DnyandevSawarkar/Mega_Project_Code/Images/arm_left.jpg

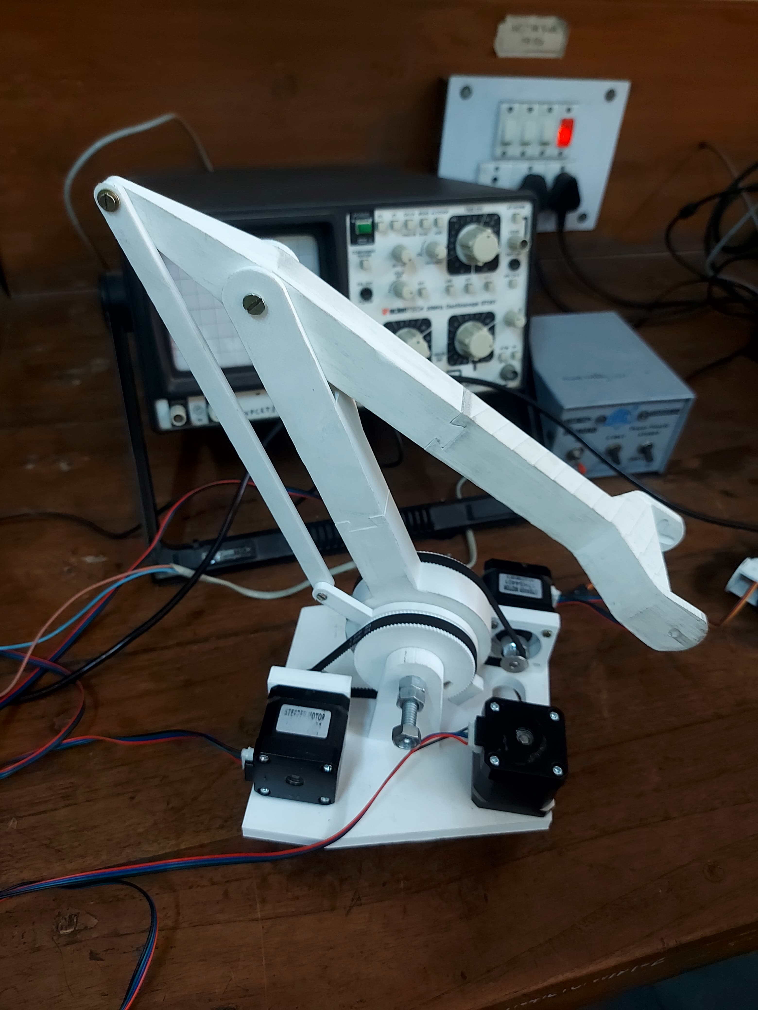
Images/arm_left.jpg
