DnyandevSawarkar/Mega_Project_Code/Images/circuit.png

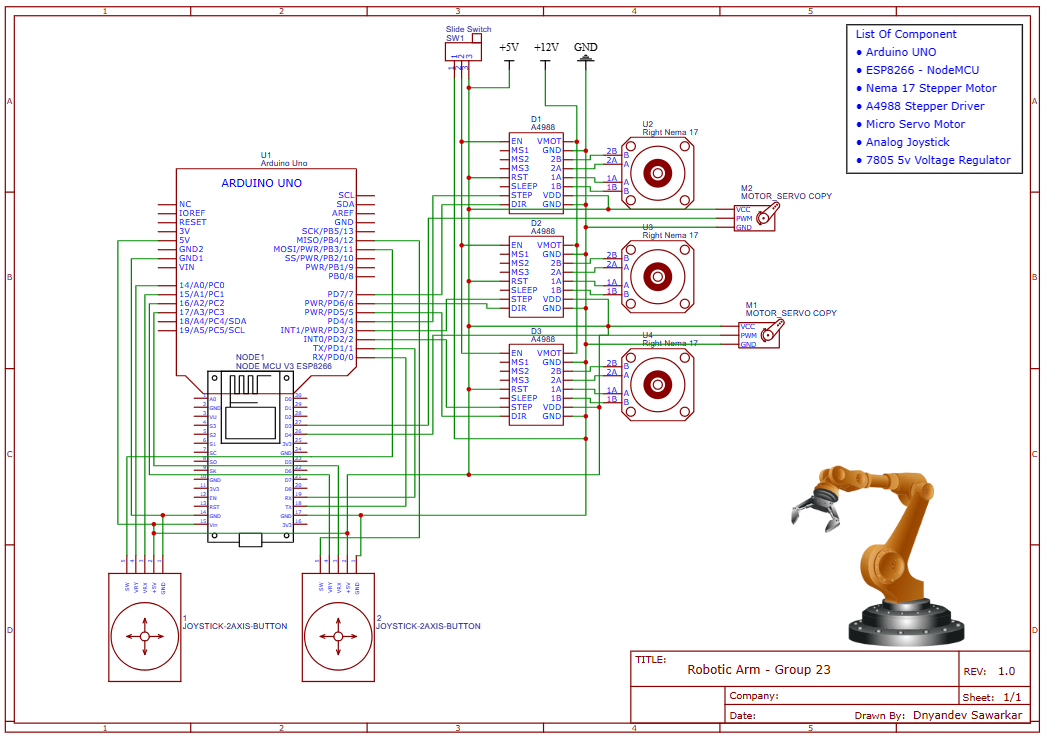
Images/circuit.png
