DnyandevSawarkar/Mega_Project_Code/Images/joystick .jpg

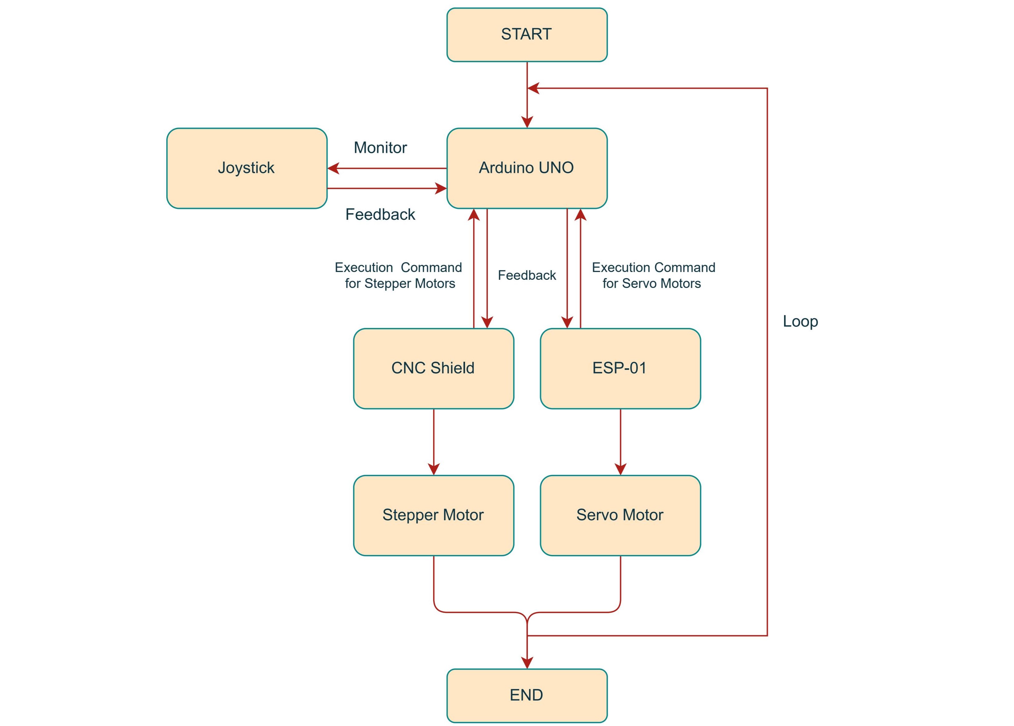
Images/joystick .jpg
