DnyandevSawarkar/Mega_Project_Code/Images/pick_place1.jpg

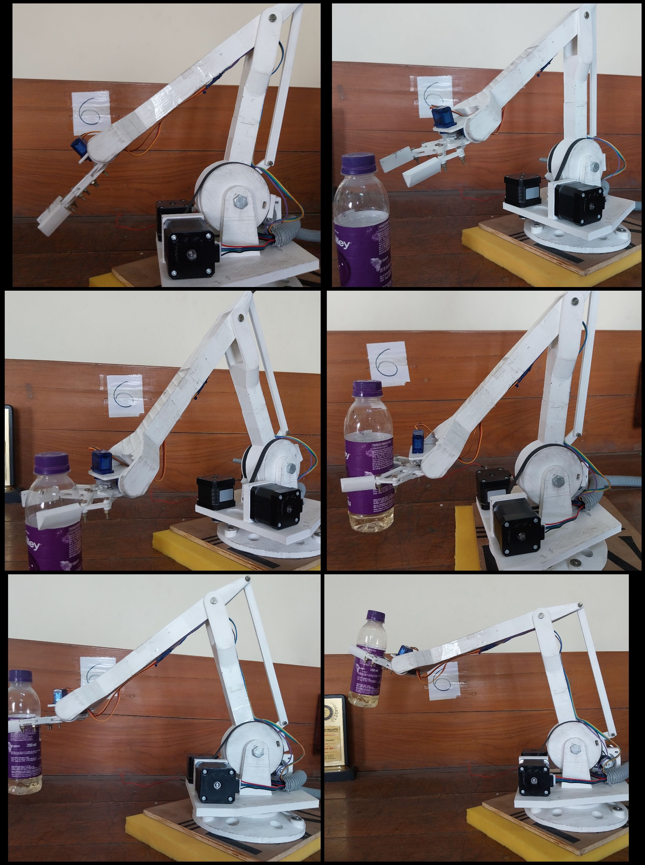
Images/pick_place1.jpg
