DnyandevSawarkar/Mega_Project_Code/Images/pick_place.jpg

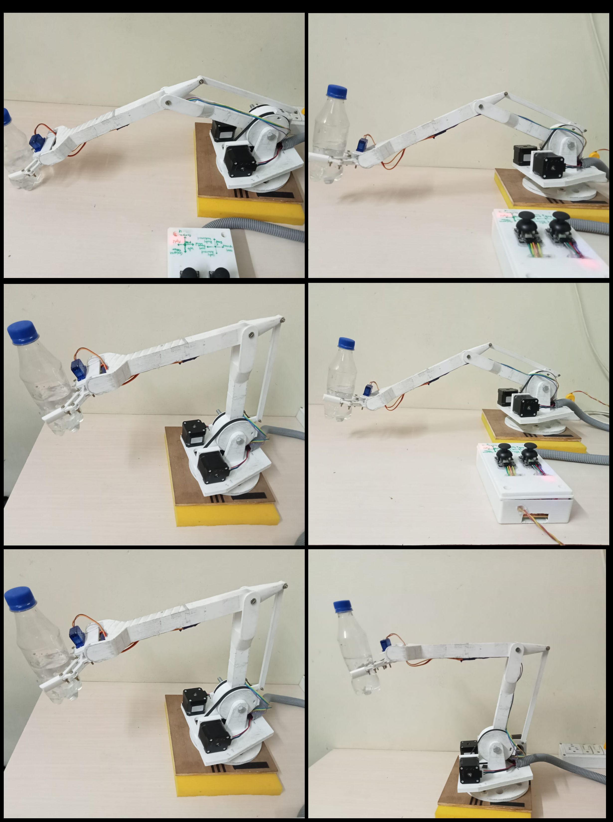
Images/pick_place.jpg
