DnyandevSawarkar/Mega_Project_Code/Images/Robotic arm block diagram.png

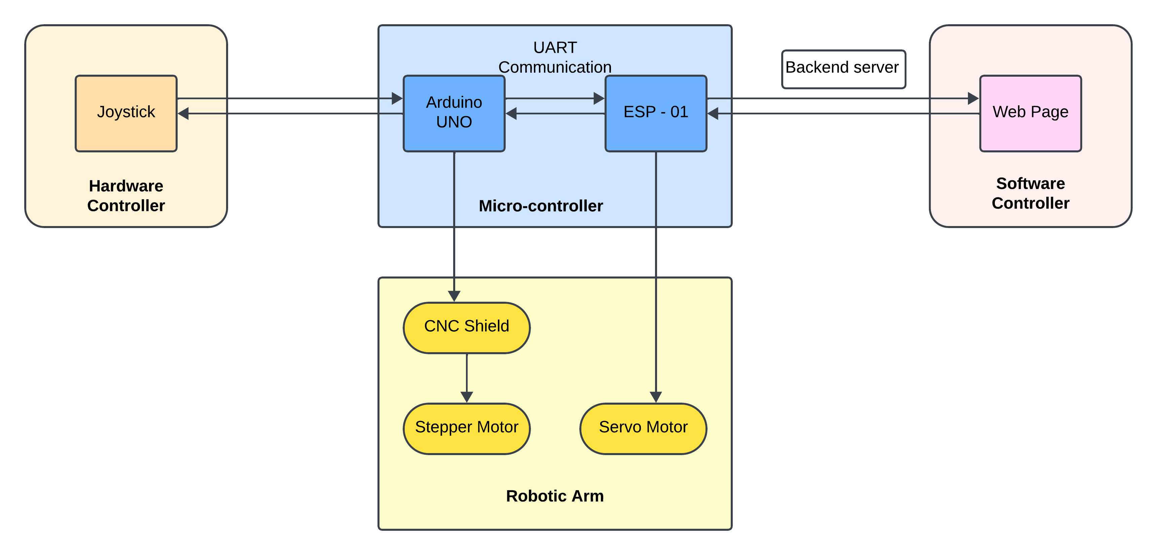
Images/Robotic arm block diagram.png
