DnyandevSawarkar/Mega_Project_Code/Images/Top_Layer.png

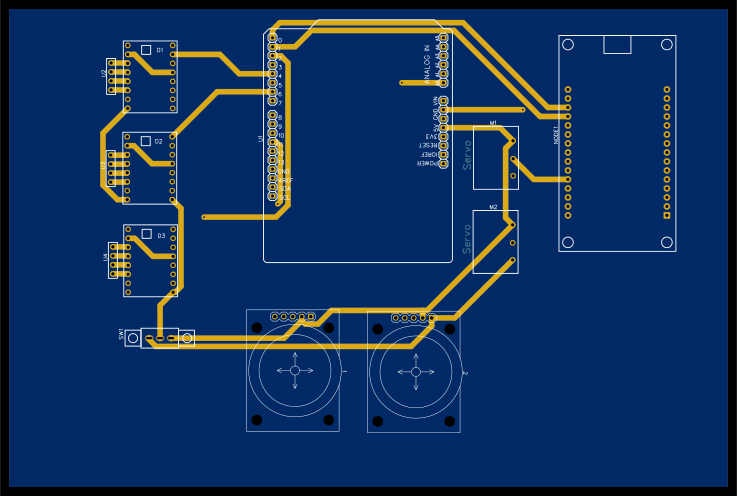
Images/Top_Layer.png
