DnyandevSawarkar/Mega_Project_Code/Body_Parts_STL/base_1.stl

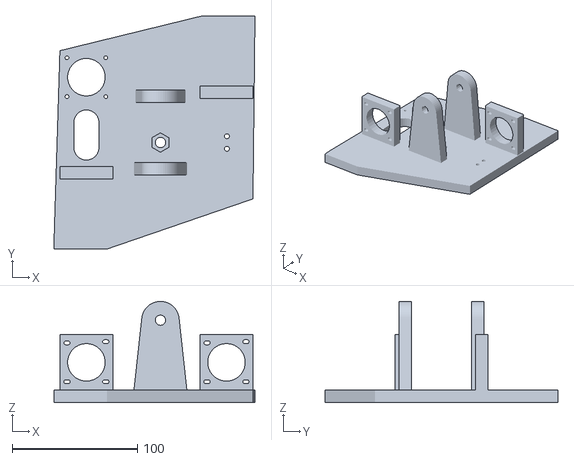
[picture p28: CAD file, 2024-04-19]
Body_Parts_STL/base_1.stl
160.2 x 186.0 x 80.8
