DnyandevSawarkar/Mega_Project_Code/Body_Parts_STL/base_2.stl

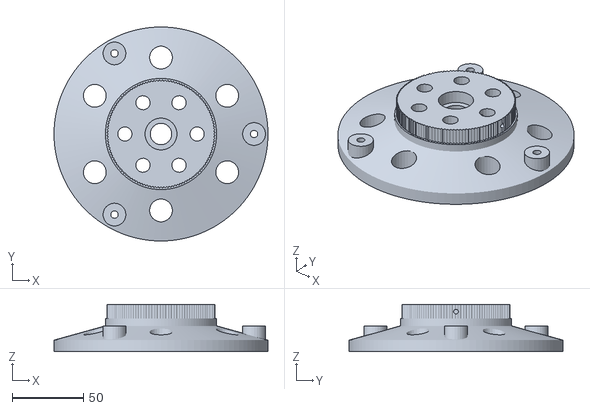
[picture p29: CAD file, 2024-04-19]
Body_Parts_STL/base_2.stl
150.0 x 150.0 x 33.0
